SP5GW/Solar_DC_Power_Backup/hw/battery/ZHehaWKKVJYNXVPWhHHH.jpg

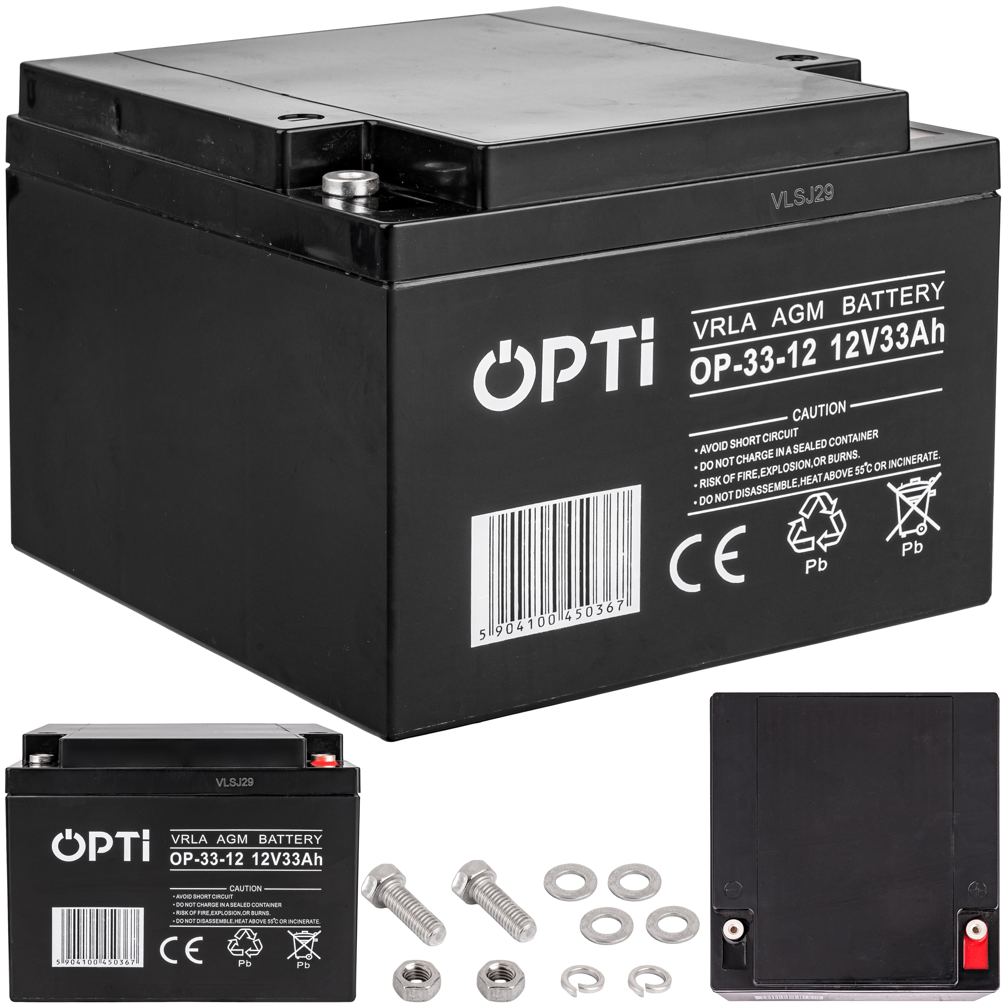
hw/battery/ZHehaWKKVJYNXVPWhHHH.jpg
