SP5GW/Solar_DC_Power_Backup/hw/solar_panel_and_regulator/YRNeHWUNNXCbSHEURKeA.jpg

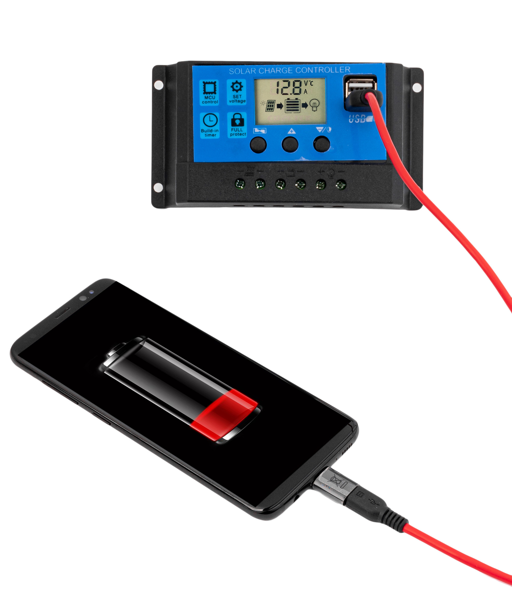
hw/solar_panel_and_regulator/YRNeHWUNNXCbSHEURKeA.jpg
