SP5GW/Solar_DC_Power_Backup/docs/solar_dc_power_backup.kicad_sch

## KiCad design docs/solar_dc_power_backup.kicad_sch (2022-12-04)

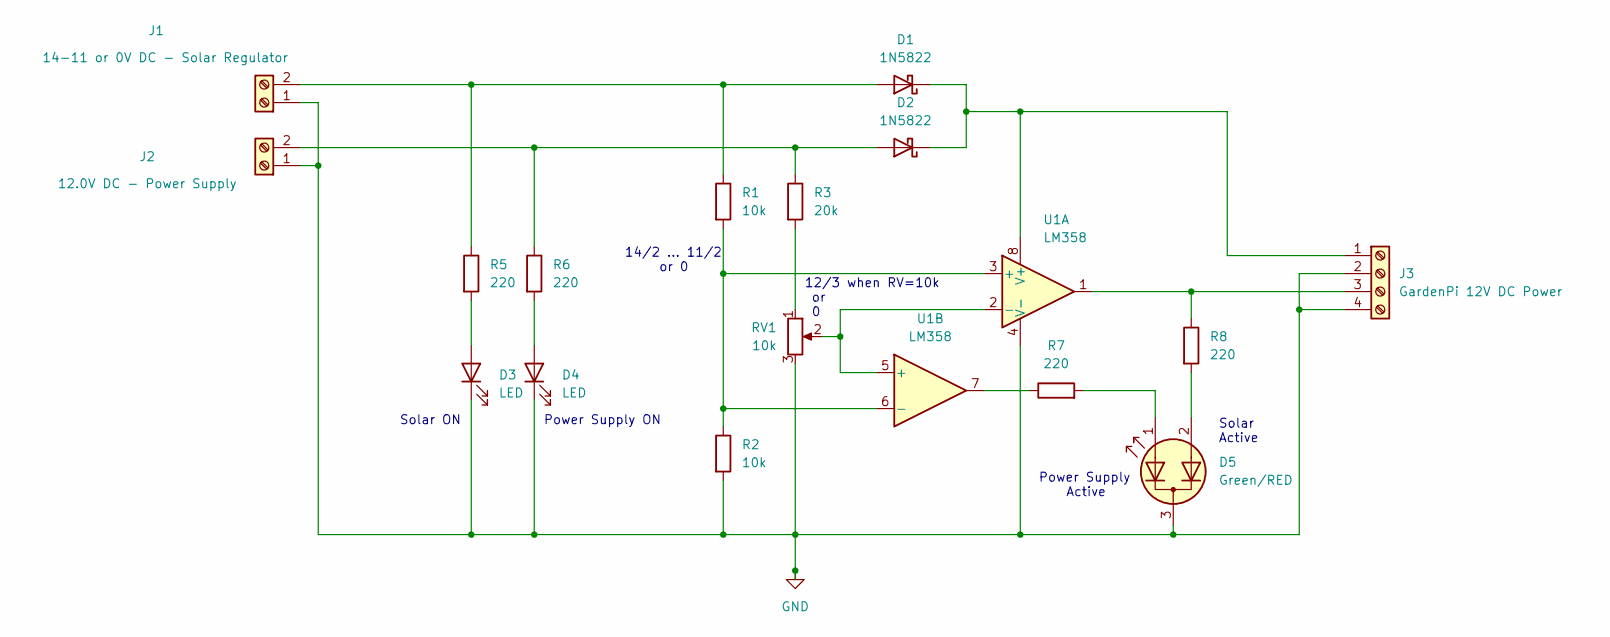
[picture p16: schematic solar_dc_power_backup.kicad_sch]

Parts:
D1, D2: 1N5822; D_5W_P10.16mm_Horizontal
D3, D4: LED
D5: Green/RED
J1: 14-11 or 0V DC - Solar Regulator; Wago_734-132_1x02_P3.50mm_Vertical
J2: 12.0V DC - Power Supply; Wago_734-132_1x02_P3.50mm_Vertical
J3: GardenPi 12V DC Power; Wago_734-134_1x04_P3.50mm_Vertical
R1, R2: 10k; R_Axial_DIN0204_L3.6mm_D1.6mm_P5.08mm_Horizontal
R3: 20k; R_Axial_DIN0204_L3.6mm_D1.6mm_P5.08mm_Horizontal
R5, R6, R7, R8: 220
RV1: 10k
U1: LM358

Connections:
GND: D3.1 (K), D4.1 (K), D5.3 (K), J1.1, J2.1, J3.2, J3.4, R2.2, RV1.3, U1.4 (V-)
unnamed: D1.1 (K), D2.1 (K), J3.1, U1.8 (V+)
unnamed: D1.2 (A), J1.2, R1.1, R5.1
unnamed: D2.2 (A), J2.2, R3.1, R6.1
unnamed: D3.2 (A), R5.2
unnamed: D4.2 (A), R6.2
unnamed: D5.1 (A1), R7.2
unnamed: D5.2 (A2), R8.2
unnamed: J3.3, R8.1, U1.1
unnamed: R1.2, R2.1, U1.3 (+), U1.6 (-)
unnamed: R3.2, RV1.1
unnamed: R7.1, U1.7
unnamed: RV1.2, U1.2 (-), U1.5 (+)

Notes on the sheet:
Power Supply Active
Solar Active
12/3 when RV=10k or 0
Power Supply ON
14/2 ... 11/2 or 0
Solar ON
